jordanlin0603/Jordan-s-Metronome-Casing-/Design Progress/SolidWorks/Solidworks 2.png

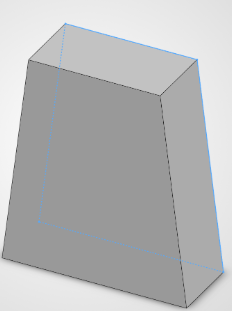
Design Progress/SolidWorks/Solidworks 2.png
