jordanlin0603/Jordan-s-Metronome-Casing-/Design Progress/SolidWorks/Solidworks 8.png

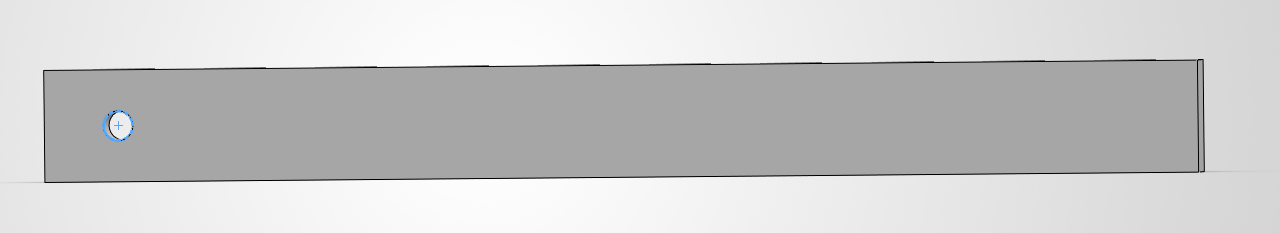
Design Progress/SolidWorks/Solidworks 8.png
