jordanlin0603/Jordan-s-Metronome-Casing-/Design Progress/SolidWorks/Solidworks 9.png

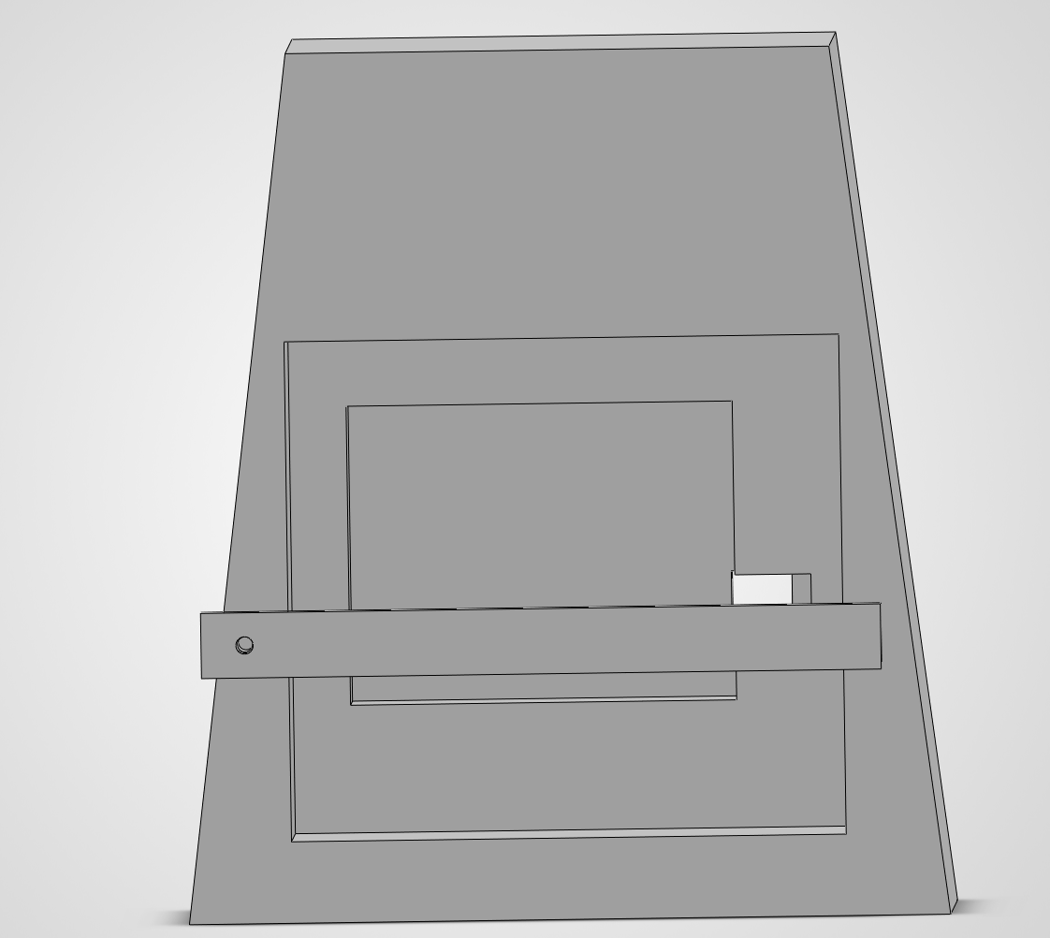
Design Progress/SolidWorks/Solidworks 9.png
