jordanlin0603/Jordan-s-Metronome-Casing-/Final Design/Metronome Back.png

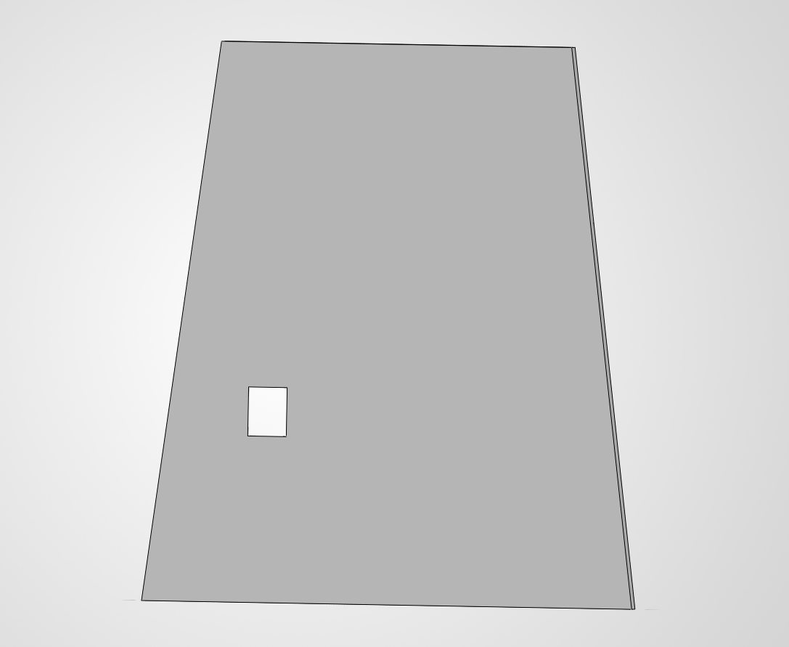
Final Design/Metronome Back.png
