jordanlin0603/Jordan-s-Metronome-Casing-/Final Design/Metronome Birds Eye View.png

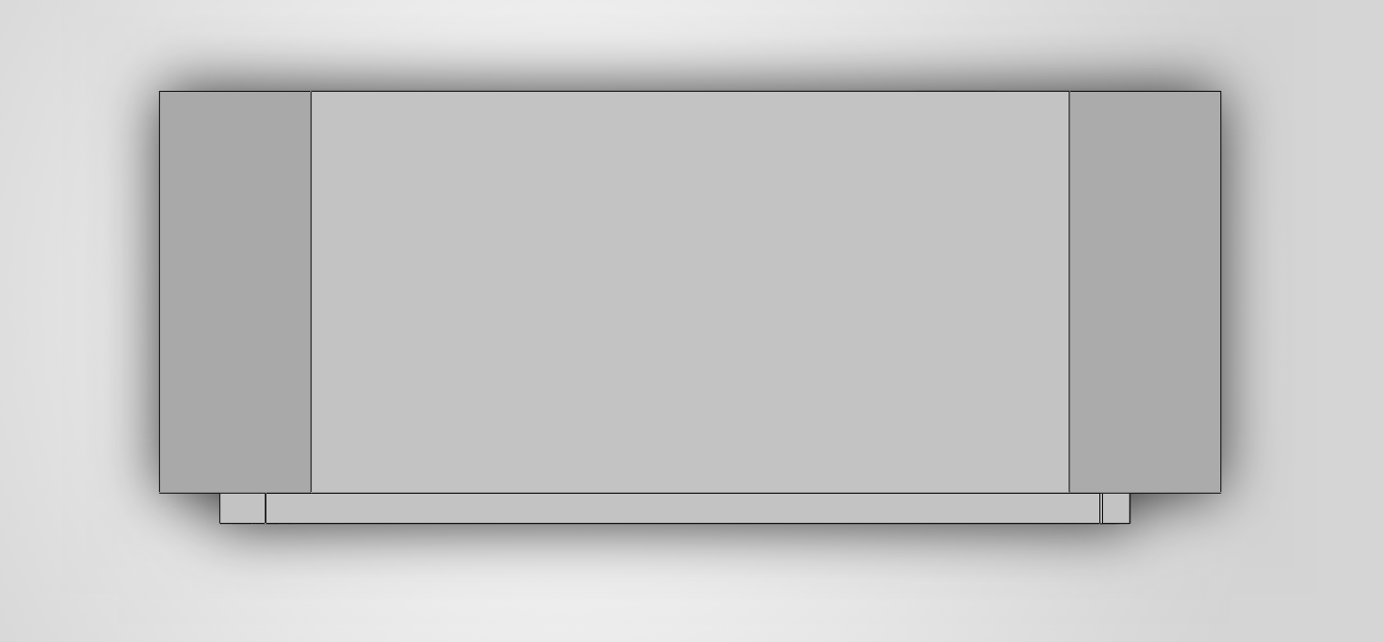
Final Design/Metronome Birds Eye View.png
