jordanlin0603/Jordan-s-Metronome-Casing-/Final Design/Metronome Front.png

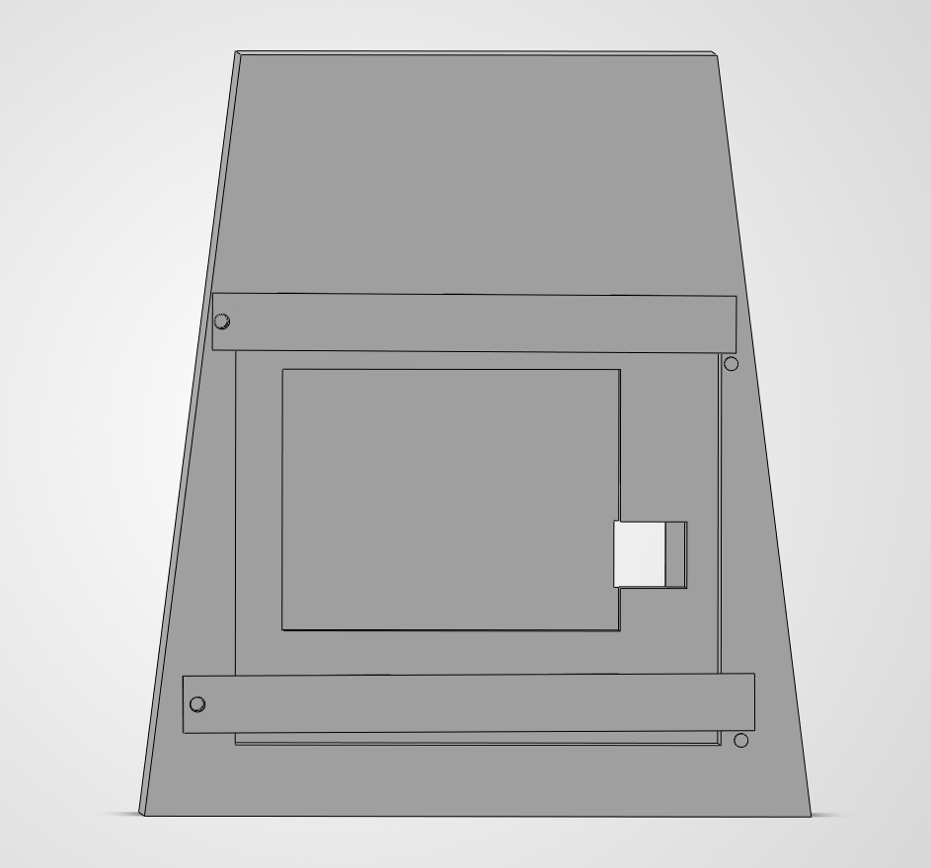
Final Design/Metronome Front.png
