jordanlin0603/Jordan-s-Metronome-Casing-/Final Design/Metronome Left.png

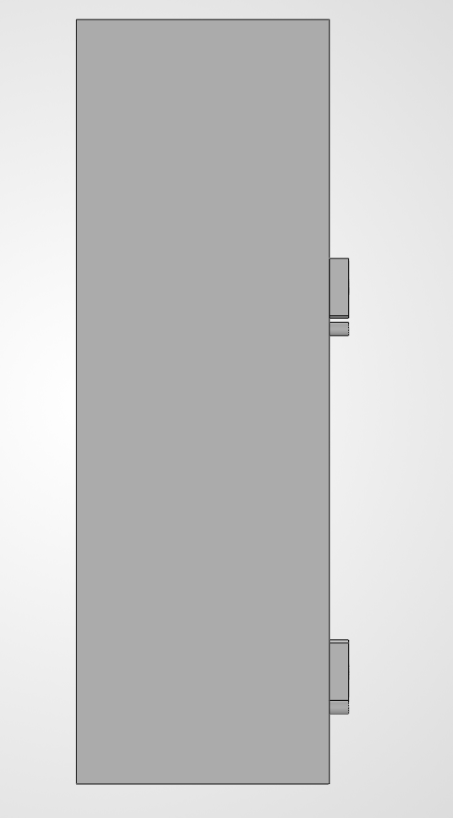
Final Design/Metronome Left.png
