jordanlin0603/Jordan-s-Metronome-Casing-/Final Design/Metronome Right Angle.png

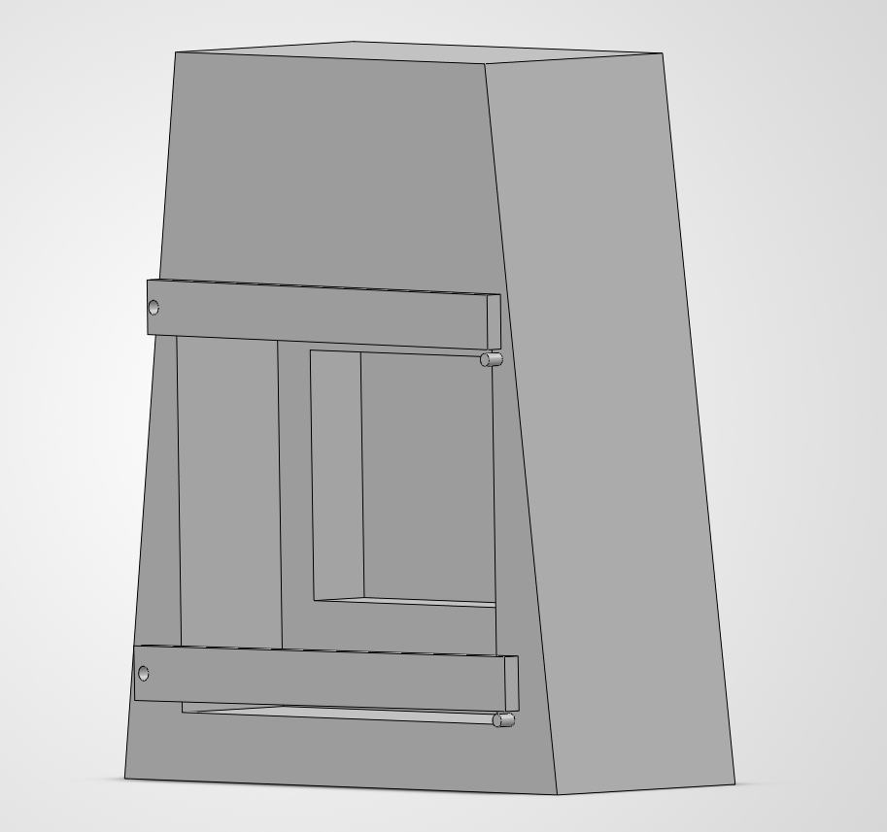
Final Design/Metronome Right Angle.png
