jordanlin0603/Jordan-s-Metronome-Casing-/Final Design/Metronome Right.png

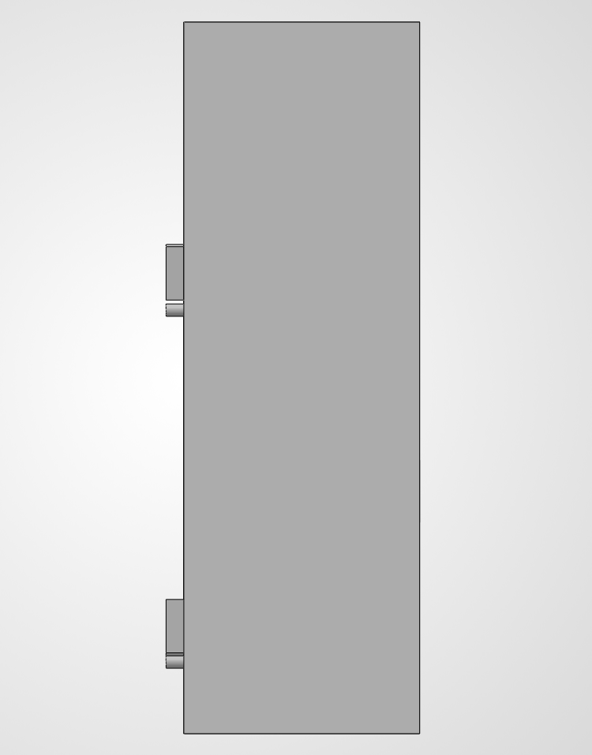
Final Design/Metronome Right.png
